RavnaPCB/01.OSOH_SOM_MB/1.DBSTM32MP1 [WIP]/Manufacturing_Data/ASSEMBLY/DBSTM32MP1-F_Fab.png

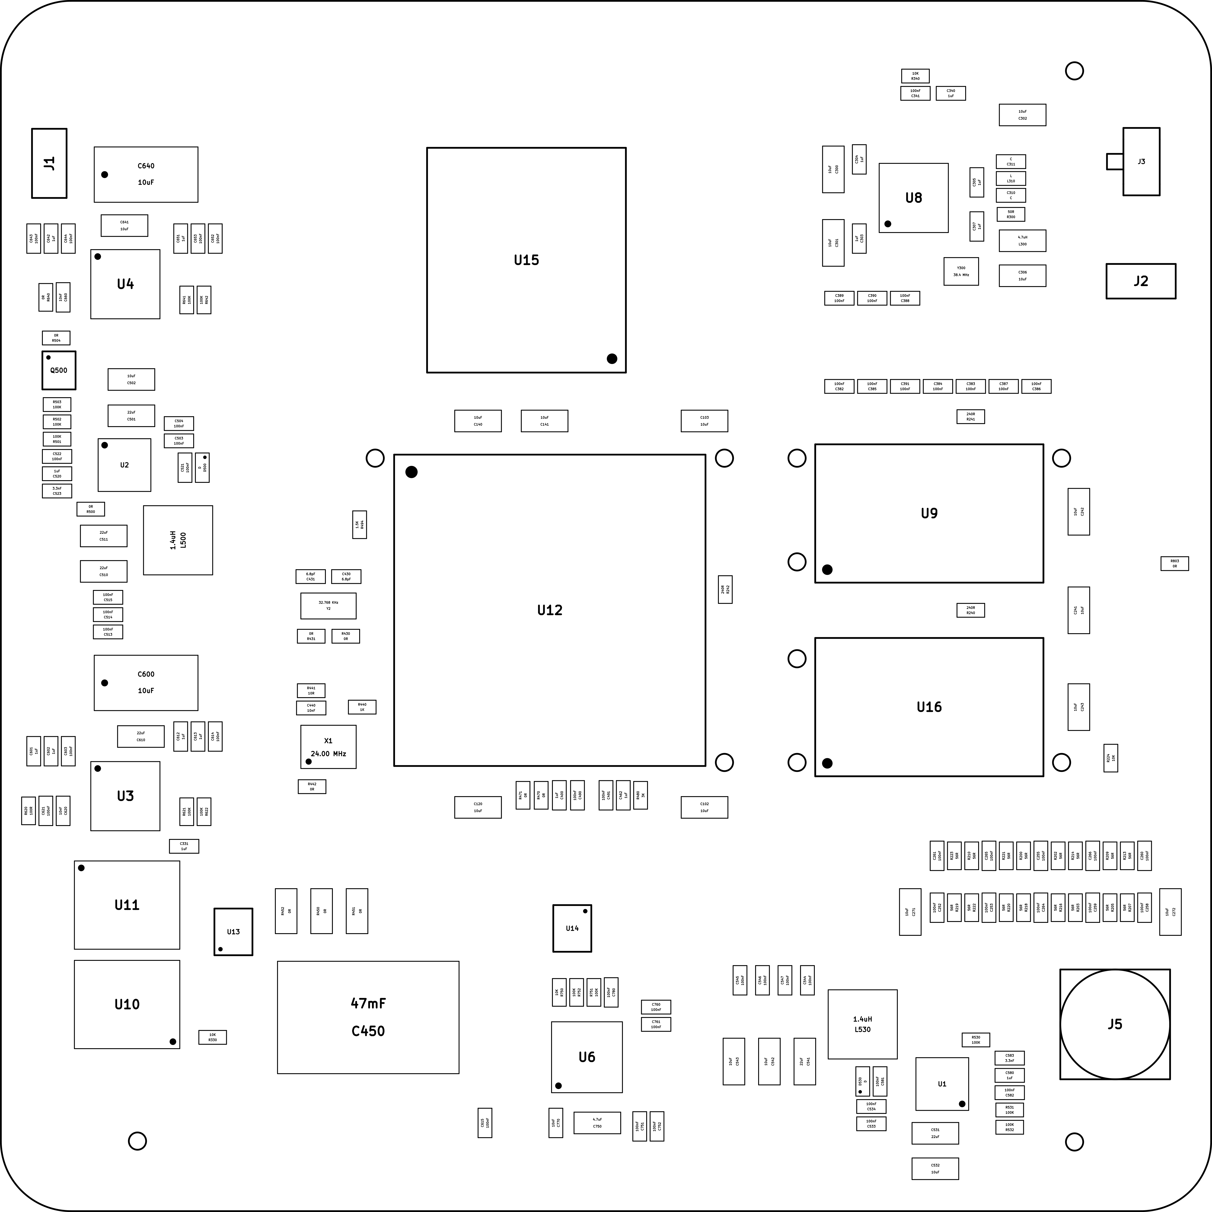
1.DBSTM32MP1 [WIP]/Manufacturing_Data/ASSEMBLY/DBSTM32MP1-F_Fab.png
