RavnaPCB/01.OSOH_SOM_MB/1.DBSTM32MP1 [WIP]/Manufacturing_Data/DP_Highlight/L3_90OHM.png

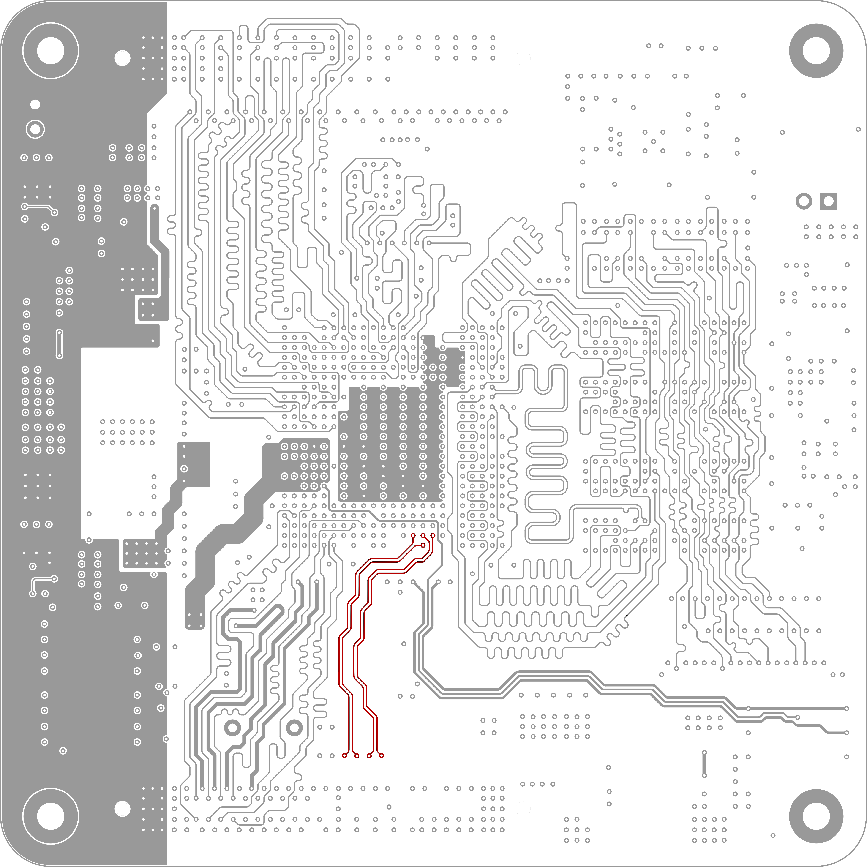
1.DBSTM32MP1 [WIP]/Manufacturing_Data/DP_Highlight/L3_90OHM.png
