RavnaPCB/01.OSOH_SOM_MB/1.DBSTM32MP1 [WIP]/HW_Development/DBSTM32MP1.kicad_sch

## KiCad design 1.DBSTM32MP1 [WIP]/HW_Development/DBSTM32MP1.kicad_sch (2022-04-24)

Schematic: DBSTM32MP1.kicad_sch

Parts:
C100, C101, C102, C103, C120, C140, C141, C241, C242, C243, C270, C271, C272, C273, C300, C301, C302, C306, C332, C502, C512, C532, C542, C543, C611, C641, C700, C710, C800: 10uF; C_0805
C104, C105, C106, C107, C108, C109, C110, C111, C112, C113, C114, C115, C116, C130, C131, C132, C133, C134, C135, C136, C142, C143, C144, C145, C146, C147, C148, C149, C150, C151, C152, C153, C154, C303, C304, C305, C307, C330, C331, C340, C400, C460, C462, C480, C520, C580, C601, C602, C612, C613, C642, C651, C701, C801: 1uF; C_0402
C200, C201, C202, C203, C204, C205, C206, C207, C208, C209, C210, C211, C212, C213, C220, C221, C222, C223, C224, C225, C226, C227, C228, C229, C230, C231, C232, C233, C240, C250, C251, C252, C253, C254, C255, C256, C257, C258, C259, C260, C261, C262, C263, C264, C265, C266, C267, C341, C350, C351, C352, C353, C354, C355, C356, C370, C371, C372, C373, C374, C375, C376, C377, C378, C379, C380, C381, C382, C383, C384, C385, C386, C387, C388, C389, C390, C391, C392, C393, C461, C470, C490, C491, C503, C504, C513, C514, C515, C521, C522, C533, C534, C544, C545, C546, C547, C581, C582, C603, C614, C615, C621, C643, C644, C652, C653, C654, C656, C702, C703, C704, C711, C712, C713, C714, C721, C751, C752, C760, C761, C780, C802, C803, C810: 100nF; C_0402
C310, C311, C820, C830: C; C_0402
C357, C360: 2.2uF; C_0805
C430, C431: 6.8pF; C_0402
C440, C620, C660, C720, C770: 10nF; C_0402
C450: 47mF; FM0H104ZF
C500, C530, C540: 22uF; CP_2312
C501, C510, C511, C531, C541, C610, C650: 22uF; C_0805
C523, C583: 3.3nF; C_0402
C600, C640: 10uF; CP_2312
C750: 4.7uF; C_0805
D420: RED; LED_0402
D421: BLUE; LED_0402
D500, D530: D; D_0402
FID1, FID2, FID3, FID4, FID5, FID6, FID7, FID8, FID9, FID10, FID11, FID12: Fiducial Marker
H1, H2, H3, H4: MountingHole_Pad; MountingHole-[2.2]-PAD-M2
J2: Connector_1x2; 1x02-Connector-[P2.00_V]
J3: Coax; CONUFL001-SMD-T
J4: uSD_693072010801
J5: Coax; SMA-132134-10
J6, J8: FX10A-120S-P-SV; FX10A-120P-SV
J7: Connector_2x5; 2x05-Connector-[P1.00_V]
L300: 4.7uH; C_0805
L310: L; C_0402
L460: 4.7uH; R_0805
L500, L530: 1.4uH; XGL-4040
Q500: N_MOSFET; SOT-323_SC-70
R200, R201, R202, R203, R204, R205, R206, R207, R208, R209, R210, R211, R212, R213, R214, R215, R216, R217, R218, R219, R220, R221, R222, R223: 56R; R_0402
R224, R225, R330, R340, R350, R351, R352, R353, R750: 10K; R_0402
R226, R620: 100R; R_0402
R240, R241, R242: 240R; R_0402
R300: 50R; R_0402
R331, R354: 22R; R_0402
R332, R355, R400, R402, R403, R405, R406, R408, R409, R410, R411, R412, R430, R431, R442, R470, R471, R500, R504, R640, R803, R900: 0R; R_0402
R401, R404, R407, R440: 1K; R_0402
R420, R421: 220R; R_0402
R441: 10R; R_0402
R450, R451, R452, R460: 0R; R_0805
R480: 3K; R_0402
R490, R491, R492, R493, R494, R495: 1.5K; R_0402
R501, R502, R503, R530, R531, R532, R621, R622, R641, R642, R721, R722, R751, R752: 100K; R_0402
R720: R100; R_0402
R800, R801: R; R_0402
TP1, TP2, TP3, TP4, TP5, TP6, TP7, TP8, TP9, TP10, TP11, TP12, TP13, TP14, TP15, TP16, TP17, TP21, TP22: TP; TP-[R0402-PAD]
TP18, TP19, TP20: TP; SP-[2.0x0.6]
U1, U2: RT6206; WDFN-10L-[3x3]-[P0.5]
U3, U4, U5: LP38798; WSON-12-[4x4]-[P0.5]
U6: LP3878-ADJ; WSON-08-[4x4]-[P0.8]
U7: LP2998; DFN-10-[3x3]-[P0.5]
U8: WF200SD; QFN-32-[4x4]-[P0.4]
U9, U16: DDR3L; TFBGA96
U10, U11: WSON-8-6x5-FLASH; WSON-08-[6x5]-[P1.27]
U12: STM32MP157AAA3
U13, U14: AND_GATE; SOT-353_SC-70-5
U15: eMMC; WFBGA153
X1: 24.00 MHz; OSC-[3.2x2.5]
Y2: 32.768 KHz; OSC-[3.2x1.5]
Y300: 38.4 MHz; OSC-[2.0x1.6]

Connections:
ADJ: C780.2, R751.1, R752.2, U6.6 (ADJ)
ANA0: U12.R4 (ANA0)
ANA1: J5.1 (In), U12.T5 (ANA1)
CPU_VDD: C120.1, C130.1, C131.1, C132.1, C133.1, C134.1, C135.1, C136.1, C353.1, C354.1, C355.1, C610.1, C611.1, C612.1, C613.1, C614.1, C615.1, R350.1, R351.1, R352.1, R353.1, R401.2, R404.2, R407.2, R409.2, R411.2, R441.2, R450.1, R460.1, R471.1, R490.1, R491.1, R492.1, R493.1, R494.1, R495.1, U3.10 (OUT_FB), U3.11 (OUT), U3.12 (OUT), U12.A14 (VDD_DSI), U12.D18 (VDD_PLL2), U12.M6 (VDD_PLL), U12.M9 (VDD), U12.N5 (VDD_ANA), U12.N8 (VDD), U12.N10 (VDD), U12.P9 (VDD), U12.P11 (VDD), U12.R10 (VDD), U12.R12 (VDD), U12.T13 (VDD), U12.U9 (VDD), U12.U12 (VDD), U12.U14 (VDD), U13.5 (VDD), U14.5 (VDD), U15.C6 (VCCQ), U15.M4 (VCCQ), U15.N4 (VCCQ), U15.P3 (VCCQ), U15.P5 (VCCQ)
DAC_EXTI9: U12.M2 (PD9)
DAC_OUT1: U12.V6 (PA4)
DAC_OUT2: U12.U5 (PA5)
DCMI_D00: J6.71, U12.E6 (PH9)
DCMI_D01[TIM5_CH1]: J6.86, U12.B1 (PH10)
DCMI_D02: J6.67, U12.C5 (PE0)
DCMI_D03: J6.73, U12.D7 (PE1)
DCMI_D04[TIM8_CH2N]: J6.65, U12.C2 (PH14)
DCMI_D05: J6.54, U12.J6 (PI4)
DCMI_D06[TIM8_CH2]: J6.64, U12.G5 (PI6)
DCMI_D07: J6.66, U12.F1 (PI7)
DCMI_D08: J6.79, U12.V11 (PH6)
DCMI_D09[TIM8_CH4]: J6.72, U12.E1 (PI2)
DCMI_D10[TIM8_ETR]: J6.76, U12.E3 (PI3)
DCMI_D11: J6.88, U12.C1 (PH15)
DCMI_D12: J6.58, U12.W8 (PF11)
DCMI_D13[TIM5_CH4]: J6.78, U12.D1 (PI0)
DCMI_HSYNC[TIM5_ETR]: J6.77, U12.D6 (PH8)
DCMI_PXCLK: J6.60, U12.W9 (PA6)
DCMI_VSYNC[TIM8_CH1]: J6.70, U12.F2 (PI5)
DDR3_A00: R200.2, U9.N3 (A00), U12.K19 (DDR_A0), U16.N3 (A00)
DDR3_A01: R201.2, U9.P7 (A01), U12.M18 (DDR_A1), U16.P7 (A01)
DDR3_A02: R202.2, U9.P3 (A02), U12.J18 (DDR_A2), U16.P3 (A02)
DDR3_A03: R203.2, U9.N2 (A03), U12.J19 (DDR_A3), U16.N2 (A03)
DDR3_A04: R204.2, U9.P8 (A04), U12.T18 (DDR_A4), U16.P8 (A04)
DDR3_A05: R205.2, U9.P2 (A05), U12.H19 (DDR_A5), U16.P2 (A05)
DDR3_A06: R206.2, U9.R8 (A06), U12.U19 (DDR_A6), U16.R8 (A06)
DDR3_A07: R207.2, U9.R2 (A07), U12.F18 (DDR_A7), U16.R2 (A07)
DDR3_A08: R208.2, U9.T8 (A08), U12.U18 (DDR_A8), U16.T8 (A08)
DDR3_A09: R209.2, U9.R3 (A09), U12.H18 (DDR_A9), U16.R3 (A09)
DDR3_A10: R210.2, U9.L7 (A10), U12.N18 (DDR_A10), U16.L7 (A10)
DDR3_A11: R211.2, U9.R7 (A11), U12.P19 (DDR_A11), U16.R7 (A11)
DDR3_A12: R212.2, U9.N7 (A12), U12.N19 (DDR_A12), U16.N7 (A12)
DDR3_A13: R213.2, U9.T3 (A13), U12.G18 (DDR_A13), U16.T3 (A13)
DDR3_A14: R214.2, U9.T7 (A14), U12.P18 (DDR_A14), U16.T7 (A14)
DDR3_A15: R215.2, U9.M7 (A15), U12.M19 (DDR_A15), U16.M7 (A15)
DDR3_BA0: R216.2, U9.M2 (BA0), U12.K20 (DDR_BA0), U16.M2 (BA0)
DDR3_BA1: R217.2, U9.N8 (BA1), U12.R18 (DDR_BA1), U16.N8 (BA1)
DDR3_BA2: R218.2, U9.M3 (BA2), U12.K18 (DDR_BA2), U16.M3 (BA2)
DDR3_CASn: R220.2, U9.K3 (CASn), U12.M22 (DDR_CASN), U16.K3 (CASn)
DDR3_CKE: R225.2, U9.K9 (CKE), U12.R19 (DDR_CKE), U16.K9 (CKE)
DDR3_CLKN: R226.2, U9.K7 (CKN), U12.N21 (DDR_CLKN), U16.K7 (CKN)
DDR3_CLKP: R226.1, U9.J7 (CKP), U12.N20 (DDR_CLKP), U16.J7 (CKP)
DDR3_CSn: R221.2, U9.L2 (CSn), U12.L18 (DDR_CSN), U16.L2 (CSn)
DDR3_DQ00: U12.E21 (DDR_DQ0), U16.E3 (DQ00)
DDR3_DQ01: U12.F21 (DDR_DQ1), U16.F7 (DQ01)
DDR3_DQ02: U12.H21 (DDR_DQ2), U16.G2 (DQ06)
DDR3_DQ03: U12.E20 (DDR_DQ3), U16.F8 (DQ03)
DDR3_DQ04: U12.J21 (DDR_DQ4), U16.H3 (DQ04)
DDR3_DQ05: U12.H20 (DDR_DQ5), U16.H7 (DQ07)
DDR3_DQ06: U12.H22 (DDR_DQ6), U16.F2 (DQ02)
DDR3_DQ07: U12.G19 (DDR_DQ7), U16.H8 (DQ05)
DDR3_DQ08: U12.N22 (DDR_DQ8), U16.D7 (DQ08)
DDR3_DQ09: U12.R21 (DDR_DQ9), U16.A7 (DQ12)
DDR3_DQ10: U12.P21 (DDR_DQ10), U16.C3 (DQ09)
DDR3_DQ11: U12.T20 (DDR_DQ11), U16.C8 (DQ10)
DDR3_DQ12: U12.V20 (DDR_DQ12), U16.C2 (DQ11)
DDR3_DQ13: U12.R20 (DDR_DQ13), U16.B8 (DQ14)
DDR3_DQ14: U12.U21 (DDR_DQ14), U16.A2 (DQ13)
DDR3_DQ15: U12.V21 (DDR_DQ15), U16.A3 (DQ15)
DDR3_DQ16: U9.D7 (DQ08), U12.B21 (DDR_DQ16)
DDR3_DQ17: U9.C3 (DQ09), U12.D21 (DDR_DQ17)
DDR3_DQ18: U9.A3 (DQ15), U12.D22 (DDR_DQ18)
DDR3_DQ19: U9.B8 (DQ14), U12.B20 (DDR_DQ19)
DDR3_DQ20: U9.C8 (DQ10), U12.A20 (DDR_DQ20)
DDR3_DQ21: U9.A7 (DQ12), U12.A21 (DDR_DQ23)
DDR3_DQ22: U9.C2 (DQ11), U12.D20 (DDR_DQ22)
DDR3_DQ23: U9.A2 (DQ13), U12.E22 (DDR_DQ21)
DDR3_DQ24: U9.E3 (DQ00), U12.V22 (DDR_DQ24)
DDR3_DQ25: U9.F7 (DQ01), U12.W20 (DDR_DQ25)
DDR3_DQ26: U9.F2 (DQ02), U12.AB21 (DDR_DQ26)
DDR3_DQ27: U9.G2 (DQ06), U12.AB20 (DDR_DQ27)
DDR3_DQ28: U9.H3 (DQ04), U12.AA21 (DDR_DQ28)
DDR3_DQ29: U9.H7 (DQ07), U12.AA20 (DDR_DQ29)
DDR3_DQ30: U9.F8 (DQ03), U12.W22 (DDR_DQ30)
DDR3_DQ31: U9.H8 (DQ05), U12.W21 (DDR_DQ31)
DDR3_DQM0: U12.G20 (DDR_DQM0), U16.E7 (LDM)
DDR3_DQM1: U12.T21 (DDR_DQM1), U16.D3 (UDM)
DDR3_DQM2: U9.D3 (UDM), U12.C22 (DDR_DQM2)
DDR3_DQM3: U9.E7 (LDM), U12.AA22 (DDR_DQM3)
DDR3_DQS0N: U12.G21 (DDR_DQS0N), U16.G3 (LDQSn)
DDR3_DQS0P: U12.G22 (DDR_DQS0P), U16.F3 (LDQS)
DDR3_DQS1N: U12.R22 (DDR_DQS1N), U16.B7 (UDQSn)
DDR3_DQS1P: U12.T22 (DDR_DQS1P), U16.C7 (UDQS)
DDR3_DQS2N: U9.B7 (UDQSn), U12.B22 (DDR_DQS2N)
DDR3_DQS2P: U9.C7 (UDQS), U12.C21 (DDR_DQS2P)
DDR3_DQS3N: U9.G3 (LDQSn), U12.Y22 (DDR_DQS3N)
DDR3_DQS3P: U9.F3 (LDQS), U12.Y21 (DDR_DQS3P)
DDR3_ODT: R223.2, U9.K1 (ODT), U12.L21 (DDR_ODT), U16.K1 (ODT)
DDR3_RASn: R219.2, U9.J3 (RASn), U12.M20 (DDR_RASN), U16.J3 (RASn)
DDR3_RESET: R224.2, U9.T2 (RESET#), U12.F19 (DDR_RESETN), U16.T2 (RESET#)
DDR3_WEn: R222.2, U9.L3 (WEn), U12.M21 (DDR_WEN), U16.L3 (WEn)
DSI_CKN: J6.105, U12.A16 (DSI_CKN)
DSI_CKP: J6.109, U12.B16 (DSI_CKP)
DSI_D0N: J6.97, U12.A15 (DSI_D0N)
DSI_D0P: J6.101, U12.B15 (DSI_D0P)
DSI_D1N: J6.113, U12.A17 (DSI_D1N)
DSI_D1P: J6.117, U12.B17 (DSI_D1P)
ETH_CLK: J8.32, U12.Y8 (PG8)
ETH_COL: J8.36, U12.T4 (PA3)
ETH_CRS: J8.40, U12.AA3 (PA0)
ETH_GTXCLK: J8.44, U12.AB4 (PG4)
ETH_MDC: J8.52, U12.AB3 (PC1)
ETH_MDIO: J8.56, U12.AB2 (PA2)
ETH_RXCLK: J8.24, U12.V4 (PA1)
ETH_RXD00: J8.31, U12.AB6 (PC4)
ETH_RXD01: J8.27, U12.AA6 (PC5)
ETH_RXD02: J8.23, U12.AB5 (PB0)
ETH_RXD03: J8.19, U12.W2 (PH7)
ETH_RXDV: J8.28, U12.Y9 (PA7)
ETH_RXER: J8.20, U12.W1 (PI10)
ETH_TXCLK: J8.51, U12.U3 (PC3)
ETH_TXD00: J8.35, U12.AA1 (PG13)
ETH_TXD01: J8.39, U12.AA2 (PG14)
ETH_TXD02: J8.43, U12.Y1 (PC2)
ETH_TXD03: J8.47, U12.Y2 (PE2)
ETH_TXEN: J8.55, U12.Y5 (PB11)
ETH_TXER: J8.48, U12.V3 (PF3)
FDCAN1_RX: J8.100, U12.Y16 (PA11)
FDCAN1_TX: J8.98, U12.W16 (PA12)
GND: C100.2, C101.2, C102.2, C103.2, C104.2, C105.2, C106.2, C107.2, C108.2, C109.2, C110.2, C111.2, C112.2, C113.2, C114.2, C115.2, C116.2, C120.2, C130.2, C131.2, C132.2, C133.2, C134.2, C135.2, C136.2, C140.2, C141.2, C142.2, C143.2, C144.2, C145.2, C146.2, C147.2, C148.2, C149.2, C150.2, C151.2, C152.2, C153.2, C154.2, C200.2, C201.2, C202.2, C203.2, C204.2, C205.2, C206.2, C207.2, C208.2, C209.2, C210.2, C211.2, C212.2, C213.2, C220.2, C221.2, C222.2, C223.2, C224.2, C225.2, C226.2, C227.2, C228.2, C229.2, C230.2, C231.2, C232.2, C233.2, C240.2, C241.2, C242.2, C243.2, C250.2, C251.2, C252.2, C253.2, C254.2, C255.2, C256.2, C257.2, C258.2, C259.2, C260.2, C261.2, C262.2, C263.2, C264.2, C265.2, C266.2, C267.2, C270.2, C271.2, C272.2, C273.2, C300.2, C301.2, C302.2, C303.2, C304.2, C305.2, C306.2, C307.2, C310.2, C311.2, C330.2, C331.2, C332.2, C340.2, C341.2, C350.2, C351.2, C352.2, C353.2, C354.2, C355.2, C356.2, C357.2, C360.1, C370.2, C371.2, C372.2, C373.2, C374.2, C375.2, C376.2, C377.2, C378.2, C379.2, C380.2, C381.2, C382.2, C383.2, C384.2, C385.2, C386.2, C387.2, C388.2, C389.2, C390.2, C391.2, C392.2, C393.2, C400.2, C430.1, C431.1, C440.2, C450.2, C460.2, C461.2, C462.1, C470.1, C480.1, C490.2, C491.2, C500.2, C501.2, C502.2, C503.2, C504.2, C510.2, C511.2, C512.2, C513.2, C514.2, C515.2, C520.2, C523.2, C530.2, C531.2, C532.2, C533.2, C534.2, C540.2, C541.2, C542.2, C543.2, C544.2, C545.2, C546.2, C547.2, C580.2, C583.2, C600.2, C601.2, C602.2, C603.2, C610.2, C611.2, C612.2, C613.2, C614.2, C615.2, C620.2, C621.2, C640.2, C641.2, C642.2, C643.2, C644.2, C650.2, C651.2, C652.2, C653.2, C654.2, C656.2, C660.2, C700.2, C701.2, C702.2, C703.2, C704.2, C710.2, C711.2, C712.2, C713.2, C714.2, C720.2, C721.2, C750.2, C751.2, C752.2, C760.2, C761.2, C770.2, C800.2, C801.2, C802.2, C803.2, C810.2, C820.2, C830.2, D420.2 (A), D421.2 (A), H1.1, H2.1, H3.1, H4.1, J2.2, J3.2 (Ext), J4.6 (VSS), J5.2 (Ext), J6.11, J6.12, J6.13, J6.14, J6.15, J6.20, J6.21, J6.26, J6.27, J6.32, J6.33, J6.38, J6.39, J6.44, J6.45, J6.50, J6.51, J6.56, J6.57, J6.62, J6.63, J6.68, J6.69, J6.74, J6.75, J6.80, J6.81, J6.84, J6.87, J6.90, J6.91, J6.93, J6.95, J6.96, J6.99, J6.102, J6.103, J6.107, J6.108, J6.111, J6.114, J6.115, J6.119, J6.120, J7.7, J7.8, J8.11, J8.12, J8.13, J8.14, J8.15, J8.16, J8.17, J8.18, J8.21, J8.22, J8.25, J8.26, J8.29, J8.30, J8.33, J8.34, J8.37, J8.38, J8.41, J8.42, J8.45, J8.46, J8.49, J8.50, J8.53, J8.54, J8.57, J8.58, J8.62, J8.63, J8.66, J8.69, J8.70, J8.74, J8.75, J8.78, J8.81, J8.82, J8.84, J8.87, J8.91, J8.93, J8.94, J8.95, J8.96, J8.97, J8.99, J8.101, J8.102, J8.103, J8.105, J8.107, J8.109, Q500.3 (D), R224.1, R225.1, R240.1, R241.1, R242.1, R300.1, R340.2, R402.2, R405.2, R408.2, R410.2, R412.2, R440.2, R470.1, R480.1, R502.1, R532.1, R622.1, R642.1, R722.1, R750.1, R752.1, TP20.1, U3.6 (GND_CP), U3.7 (GND), U3.13 (GND), U4.6 (GND_CP), U4.7 (GND), U4.13 (GND), U5.6 (GND_CP), U5.7 (GND), U5.13 (GND), U6.3 (GND), U7.3 (AGND), U7.8 (PGND), U7.11 (PAD), U8.10 (GND), U8.14 (RESERVE_1), U8.33 (GND), U9.A9 (VSS), U9.B1 (VSSQ), U9.B3 (VSS), U9.B9 (VSSQ), U9.D1 (VSSQ), U9.D8 (VSSQ), U9.E1 (VSS), U9.E2 (VSSQ), U9.E8 (VSSQ), U9.F9 (VSSQ), U9.G1 (VSSQ), U9.G8 (VSS), U9.G9 (VSSQ), U9.J2 (VSS), U9.J8 (VSS), U9.M1 (VSS), U9.M9 (VSS), U9.P1 (VSS), U9.P9 (VSS), U9.T1 (VSS), U9.T9 (VSS), U10.4 (GND), U11.4 (GND), U12.A1 (VSS), U12.A19 (VSS), U12.A22 (VSS), U12.AA4 (VSS), U12.AA13 (VSS_USBHS), U12.AA16 (VSS_USBHS), U12.AA18 (VSS), U12.AB1 (VSS), U12.AB18 (VSS), U12.AB22 (VSS), U12.B2 (VSS), U12.B19 (VSS), U12.C3 (VSS), U12.C8 (VSS), U12.C11 (VSS), U12.C14 (VSS_DSI), U12.C15 (VSS_DSI), U12.C16 (VSS_DSI), U12.C17 (VSS_DSI), U12.C18 (VSS_DSI), U12.C19 (VSS), U12.C20 (VSS), U12.D4 (VSS), U12.D19 (VSS_PLL2), U12.E5 (VSS), U12.E19 (VSS), U12.F6 (VSS), U12.F7 (VSS), U12.F8 (VSS), U12.F16 (VSS), U12.F20 (VSS), U12.G4 (VSS), U12.G6 (VSS), U12.G8 (VSS), U12.G10 (VSS), U12.G12 (VSS), U12.G14 (VSS), U12.G17 (VSS), U12.H7 (VSS), U12.J9 (VSS), U12.J11 (VSS), U12.J13 (VSS), U12.J17 (VSS), U12.J20 (VSS), U12.K3 (VSS), U12.K7 (VSS), U12.K10 (VSS), U12.K12 (VSS), U12.K14 (VSS), U12.L9 (VSS), U12.L11 (VSS), U12.L13 (VSS), U12.L17 (VSS), U12.L19 (VSS), U12.L20 (VSS), U12.M5 (VSS_PLL), U12.M7 (VSS), U12.M10 (VSS), U12.M12 (VSS), U12.M14 (VSS), U12.N6 (VREF-), U12.N9 (VSS), U12.N11 (VSS), U12.N13 (VSS), U12.N17 (VSS), U12.P3 (VSS), U12.P5 (VSS_ANA), U12.P7 (VSS), U12.P10 (VSS), U12.P12 (VSS), U12.P14 (VSS), U12.P20 (VSS), U12.R6 (VSSA), U12.R8 (VSS), U12.R17 (VSS), U12.T6 (VSSA), U12.T7 (VSS), U12.T9 (VSS), U12.T11 (VSS), U12.T19 (VSS), U12.U6 (VSSA), U12.U7 (VSS), U12.U13 (VSS), U12.U15 (VSS), U12.U17 (VSS), U12.U20 (VSS), U12.V5 (VSS), U12.V16 (VSS), U12.V18 (VSS), U12.V19 (VSS), U12.W17 (VSS), U12.W19 (VSS), U12.Y3 (VSS), U12.Y7 (VSS), U12.Y10 (VSS), U12.Y13 (VSS_USBHS), U12.Y14 (VSS_USBHS), U12.Y15 (VSS_USBHS), U12.Y18 (VSS), U12.Y20 (VSS), U13.3 (GND), U14.3 (GND), U15.A6 (VSS), U15.C4 (VSSQ), U15.E7 (VSS), U15.G5 (VSS), U15.H10 (VSS), U15.J5 (VSS), U15.K8 (VSS), U15.N2 (VSSQ), U15.N5 (VSSQ), U15.P4 (VSSQ), U15.P6 (VSSQ), U16.A9 (VSS), U16.B1 (VSSQ), U16.B3 (VSS), U16.B9 (VSSQ), U16.D1 (VSSQ), U16.D8 (VSSQ), U16.E1 (VSS), U16.E2 (VSSQ), U16.E8 (VSSQ), U16.F9 (VSSQ), U16.G1 (VSSQ), U16.G8 (VSS), U16.G9 (VSSQ), U16.J2 (VSS), U16.J8 (VSS), U16.M1 (VSS), U16.M9 (VSS), U16.P1 (VSS), U16.P9 (VSS), U16.T1 (VSS), U16.T9 (VSS), X1.2 (GND), Y300.2, Y300.4
GPIO[TIM8_CH3N]: J6.82, U12.E7 (PK1)
GPIO_00[BOTTOM]: U12.W5 (PG0)
GPIO_00[TOP]: U12.H3 (PZ7)
GPIO_01[BOTTOM]: U12.Y4 (PG1)
GPIO_01[TOP]: U12.J5 (PI9)
GPIO_02[BOTTOM]: U12.W4 (PG2)
GPIO_02[TOP]: U12.K6 (PJ11)
GPIO_03[BOTTOM]: U12.U4 (PG3)
GPIO_03[TOP]: U12.L3 (PD6)
GPIO_04[BOTTOM]: U12.AA5 (PB1)
GPIO_04[TOP]: U12.M1 (PD8)
GPIO_05[BOTTOM]: U12.W7 (PF13)
GPIO_05[TOP]: U12.M3 (PD14)
GPIO_06[BOTTOM]: U12.U8 (PG5)
GPIO_06[TOP]: U12.L1 (PD15)
GPIO_07[BOTTOM]: U12.V8 (PF12)
GPIO_07[TOP]: U12.K2 (PJ4)
GPIO_08[BOTTOM]: U12.AA8 (PB5)
GPIO_08[TOP]: U12.K1 (PJ5)
GPIO_09[BOTTOM]: U12.AB8 (PB8)
GPIO_09[TOP]: U12.L5 (PJ6)
GPIO_10[BOTTOM]: U12.AB9 (PD11)
GPIO_10[TOP]: U12.L2 (PJ9)
GPIO_11[BOTTOM]: U12.W10 (PE7)
GPIO_11[TOP]: U12.C7 (PJ15)
GPIO_12[BOTTOM]: U12.W11 (PE9)
GPIO_13[BOTTOM]: U12.Y12 (PE8)
GPIO_14[BOTTOM]: U12.V14 (PD13)
GPIO_15[BOTTOM]: U12.W14 (PE10)
GPIO_16[BOTTOM]: U12.W15 (PG9)
GPIO_FEM_1: TP11.1, U8.1 (GPIO/FEM_1)
GPIO_FEM_2: TP12.1, U8.2 (GPIO/FEM_2)
GPIO_FEM_3: TP13.1, U8.3 (GPIO/FEM_3)
GPIO_FEM_4: TP14.1, U8.4 (GPIO/FEM_4)
GPIO_FEM_5: TP15.1, U8.17 (GPIO/FEM_5)
GPIO_FEM_6: TP16.1, U8.18 (GPIO/FEM_6)
GPIO_FEM_PDET: TP10.1, U8.5 (GPIO/FEM_PDET)
GPIO_PTA_FREQ: TP6.1, U8.22 (GPIO/PTA_FREQ)
GPIO_PTA_RF_ACT: TP8.1, U8.20 (GPIO/PTA_RF_ACT)
GPIO_PTA_STATUS: TP7.1, U8.21 (GPIO/PTA_STATUS)
GPIO_PTA_TX_CONF: TP9.1, U8.19 (GPIO/PTA_TX_CONF)
HDMI-CEC: J6.61, U12.E11 (PA15)
I2C1_SCL: J8.60, R490.2, U12.V7 (PF14)
I2C1_SDA: J8.64, R491.2, U12.W6 (PF15)
I2C2_SCL: J6.83, R492.2, U12.A3 (PH4)
I2C2_SDA: J6.85, R493.2, U12.A2 (PH5)
I2C4_SCL: J6.112, R494.2, U12.G1 (PZ4)
I2C4_SDA: J6.110, R495.2, U12.H4 (PZ5)
I2S1_CK: J6.89, U12.G2 (PZ0)
I2S1_MCK: J6.100, U12.G3 (PZ6)
I2S1_SDI: J6.94, U12.H5 (PZ1)
I2S1_SDO: J6.98, U12.K5 (PZ2)
I2S1_WS: J6.92, U12.F4 (PZ3)
I2S_CLKIN: U12.T3 (PI11)
JTCK-SWCLK: J7.4, U12.D17 (JTCK-SWCLK)
JTDI: J7.1, U12.D16 (JTDI)
JTDO-TRACESWO: J7.3, U12.E16 (JTDO-TRACESWO)
JTMS-SWDIO: J7.6, U12.E17 (JTMS-SWDIO)
LTDC-B00: J6.40, U12.B8 (PJ12)
LTDC-B01: J6.42, U12.J4 (PG12)
LTDC-B02: J6.41, U12.B7 (PJ14)
LTDC-B03: J6.59, U12.A8 (PD10)
LTDC-B04: J6.46, U12.B6 (PK3)
LTDC-B05: J6.48, U12.A6 (PK4)
LTDC-B06: J6.47, U12.C6 (PK5)
LTDC-B07: J6.49, U12.A5 (PK6)
LTDC-CLK: J6.37, U12.D2 (PI14)
LTDC-DE: J6.53, U12.B5 (PK7)
LTDC-G00: J6.28, U12.L4 (PJ7)
LTDC-G01: J6.30, U12.H6 (PJ8)
LTDC-G02[TIM8_CH1N]: J6.36, U12.D3 (PH13)
LTDC-G03: J6.31, U12.J3 (PJ10)
LTDC-G04: J6.34, U12.A7 (PJ13)
LTDC-G05[TIM8_CH3]: J6.55, U12.D8 (PK0)
LTDC-G06[TIM8_BKIN2]: J6.35, U12.E2 (PI1)
LTDC-G07[TIM8_BKIN1]: J6.52, U12.E8 (PK2)
LTDC-HSYNC: J6.25, U12.H2 (PI12)
LTDC-R00: J6.16, U12.F3 (PI15)
LTDC-R01: J6.18, U12.J2 (PJ0)
LTDC-R02: J6.17, U12.L6 (PJ1)
LTDC-R03: J6.19, U12.K4 (PJ2)
LTDC-R04: J6.22, U12.J1 (PJ3)
LTDC-R05[TIM5_CH2]: J6.43, U12.B3 (PH11)
LTDC-R06[TIM5_CH3]: J6.23, U12.F5 (PH12)
LTDC-R07: J6.24, U12.C4 (PE15)
LTDC-VSYNC: J6.29, U12.H1 (PI13)
NJTRST: J7.5, U12.E15 (NJTRST)
NRST: J8.89, R900.2, U12.R2 (NRST), U13.2
NRST_CORE: R900.1, U12.R1 (NRST_CORE)
unnamed: C306.1, C307.1, L300.2, U8.9 (VDD_RF)
unnamed: C310.1, L310.2, U8.12 (RF_2)
unnamed: C311.1, J3.1 (In), L310.1
unnamed: C356.1, C357.1, U15.C2 (VDDI)
unnamed: C400.1, TP21.1, U12.AB12 (VDDA1V8_REG), U14.1, U14.2
unnamed: C430.2, R430.2, Y2.2
unnamed: C431.2, R431.2, Y2.1
unnamed: C450.1, R451.1
unnamed: C462.2, U12.AB17 (VDDA1V1_REG)
unnamed: C470.2, U12.B14 (VDDA1V8_DSI)
unnamed: C480.2, U12.A18 (VDD1V2_DSI_PHY), U12.B18 (VDD1V2_DSI_REG)
unnamed: C521.2, D500.1 (K), U2.8 (BOOT)
unnamed: C522.2, R501.1, R502.2, R503.2, U2.2 (FB)
unnamed: C581.2, D530.1 (K), U1.8 (BOOT)
unnamed: C582.2, R531.1, R532.2, U1.2 (FB)
unnamed: C620.1, U3.4 (CP)
unnamed: C621.1, R620.1, U3.5 (EN)
unnamed: C660.1, U4.4 (CP)
unnamed: C720.1, U5.4 (CP)
unnamed: C721.1, R720.1, U5.5 (EN)
unnamed: C770.1, U6.1 (Bypass)
unnamed: C820.1, R800.1, U7.2 (BIAS)
unnamed: C830.1, R801.1, U7.4 (VDDQ)
unnamed: D420.1 (K), R420.1
unnamed: D421.1 (K), R421.1
unnamed: Q500.1 (G), R504.2
unnamed: Q500.2 (S), R503.1
unnamed: R240.2, U16.L8 (ZQ)
unnamed: R241.2, U9.L8 (ZQ)
unnamed: R242.2, U12.K22 (DDR_ZQ)
unnamed: R300.2, U8.11 (RF_1)
unnamed: R331.1, U12.V12 (PF10)
unnamed: R332.2, U12.U10 (PC0)
unnamed: R351.2, R354.1, U15.M6 (CLK)
unnamed: R353.2, R355.2, U15.K5 (RSTn)
unnamed: R400.1, U12.N3 (BOOT0)
unnamed: R400.2, R401.1, R402.1
unnamed: R403.1, U12.N4 (BOOT1)
unnamed: R403.2, R404.1, R405.1
unnamed: R406.1, U12.P4 (BOOT2)
unnamed: R406.2, R407.1, R408.1
unnamed: R420.2, U12.W3 (PA13)
unnamed: R421.2, U12.R3 (PA14)
unnamed: R430.1, U12.P1 (PC14-OSC32_IN)
unnamed: R431.1, U12.P2 (PC15-OSC32_OUT)
unnamed: R440.1, U12.T2 (PH1-OSC_OUT)
unnamed: R442.1, X1.1 (EN)
unnamed: R470.2, R471.2, U12.AA12 (BYPASS_REG1V8)
unnamed: R500.1, TP2.1, U2.5 (PGOOD)
unnamed: R530.1, TP1.1, U1.5 (PGOOD)
unnamed: R621.1, R622.2, U3.8 (FB)
unnamed: R621.2, U3.9 (SET)
unnamed: R640.1, U4.5 (EN)
unnamed: R641.1, R642.2, U4.8 (FB)
unnamed: R641.2, U4.9 (SET)
unnamed: R721.1, R722.2, U5.8 (FB)
unnamed: R721.2, U5.9 (SET)
unnamed: TP17.1, U8.23 (LP_CLK)
unnamed: U8.7 (XTAL_I), Y300.1
unnamed: U8.8 (XTAL_O), Y300.3
unnamed: U12.T1 (PH0-OSC_IN), X1.3 (OUT)
OSC_VDD: C440.1, R441.1, X1.4 (VDD)
PDR_ON: R409.1, R410.1, U12.V2 (PDR_ON)
PDR_ON_CORE: R411.1, R412.1, U12.U2 (PDR_ON_CORE)
PG: TP5.1, U7.5 (PG)
PWR_LP: R504.1, U12.U1 (PWR_LP)
PWR_ON: R442.2, U2.1 (EN), U12.V1 (PWR_ON), U13.1
PWR_ONRST: R640.2, U1.1 (EN), U7.7 (EN), U13.4
QUADSPI_BK1_IO00: U10.5 (IO0), U12.AB10 (PF8)
QUADSPI_BK1_IO01: U10.2 (IO1), U12.AB11 (PF9)
QUADSPI_BK1_IO02: U10.3 (IO2), U12.AA10 (PF7)
QUADSPI_BK1_IO03: U10.7 (IO3), U12.AA11 (PF6)
QUADSPI_BK1_NCS: R330.2, R332.1, U10.1 (CS), U11.1 (CS), U12.W13 (PB6)
QUADSPI_BK2_IO00: U11.5 (IO0), U12.AB7 (PH2)
QUADSPI_BK2_IO01: U11.2 (IO1), U12.Y6 (PH3)
QUADSPI_BK2_IO02: U11.3 (IO2), U12.AA9 (PG10)
QUADSPI_BK2_IO03: U11.7 (IO3), U12.Y11 (PG7)
QUADSPI_CLK: R331.2, U10.6 (CLK), U11.6 (CLK)
SDMMC1_CDIR: U12.F12 (PB9)
SDMMC1_CK: J4.5 (CLK), R340.1, U12.E12 (PC12)
SDMMC1_CKIN: U12.F15 (PE4)
SDMMC1_CMD: J4.3 (CMD), U12.D12 (PD2)
SDMMC1_D00: J4.7 (DAT0), U12.E14 (PC8)
SDMMC1_D01: J4.8 (DAT1), U12.D14 (PC9)
SDMMC1_D02: J4.1 (DATA2), U12.E9 (PE6)
SDMMC1_D03: J4.2 (DATA3), U12.D15 (PC11)
SDMMC1_D123DIR: U12.F14 (PC10)
SDMMC2_CK: R354.2, U12.A10 (PE3)
SDMMC2_CMD: R352.2, U12.D11 (PG6), U15.M5 (CMD)
SDMMC2_D00: R350.2, U12.A13 (PB14), U15.A3 (DATA0)
SDMMC2_D01: U12.B12 (PB15), U15.A4 (DATA1)
SDMMC2_D02: U12.A12 (PB3), U15.A5 (DATA2)
SDMMC2_D03: U12.C13 (PB4), U15.B2 (DATA3)
SDMMC2_D04: U12.B13 (PA8), U15.B3 (DATA4)
SDMMC2_D05: U12.A11 (PA9), U15.B4 (DATA5)
SDMMC2_D06: U12.C12 (PE5), U15.B5 (DATA6)
SDMMC2_D07: U12.B11 (PD3), U15.B6 (DATA7)
SDMMC2_RES: R355.1, U12.F11 (PB7)
SDMMC3_CDIR: U8.24 (GPIO_WIRQ), U12.B9 (PF1)
SDMMC3_CK: U8.26 (SDIO_CLK/SPI_CLK), U12.D10 (PG15)
SDMMC3_CKIN: U12.E10 (PF0)
SDMMC3_CMD: U8.27 (SDIO_CMD/SPI_MOSI), U12.C10 (PD0)
SDMMC3_D00: U8.28 (SDIO_DAT0/SPI_MISO), U12.B10 (PD1)
SDMMC3_D0DIR: U8.16 (GPIO/WUP), U12.F13 (PF2)
SDMMC3_D01: U8.29 (SDIO_DAT1/SPI_WIRQ), U12.C9 (PD4)
SDMMC3_D02: U8.30 (SDIO_DAT2/HIF_SEL), U12.A9 (PD5)
SDMMC3_D03: U8.31 (SDIO_DAT3/SPI_CSN), U12.F10 (PD7)
SDMMC3_D123DIR: U8.15 (RESETN), U12.F9 (PF4)
SDMMC3_RESET?: U12.D9 (PF5)
SPI4_MISO: J6.118, U12.A4 (PE13)
SPI4_MOSI: J6.116, U12.B4 (PE14)
SPI4_NSS: J6.104, U12.D5 (PE11)
SPI4_SCK: J6.106, U12.E4 (PE12)
SS: C583.1, U1.4 (SS)
SS1: C523.1, U2.4 (SS)
SW1: C581.1, L530.1, TP3.1, U1.6 (SW), U1.7 (SW)
SW2: C521.1, L500.1, TP4.1, U2.6 (SW), U2.7 (SW)
TP1: U12.AA19 (DDR_ATO)
TP2: U12.L22 (DDR_DTO0)
TP3: U12.K21 (DDR_DTO1)
USART3_CTS: J8.79, U12.V10 (PB13)
USART3_RTS: J8.77, U12.W12 (PD12)
USART3_RX: J8.73, U12.AA7 (PB12)
USART3_TX: J8.71, U12.V9 (PB10)
USART4_RX: TP18.1, U12.V13 (PB2)
USART4_TX: TP19.1, U12.U11 (PG11)
USART6_RX: J7.9, U12.D13 (PC7)
USART6_TX: J7.10, U12.E13 (PC6)
USB_D1+: J8.76, U12.AA15 (USB_DP1)
USB_D1-: J8.80, U12.AB15 (USB_DM1)
USB_D2+: J8.72, U12.AB14 (USB_DP2)
USB_D2-: J8.68, U12.AA14 (USB_DM2)
USB_OTG_ID: J8.83, U12.Y17 (PA10)
USB_REG_EN: R750.2, TP22.1, U6.8 (SD), U14.4
USB_RREF: R480.2, U12.AA17 (USB_RREF)
USB_VBUS: J8.85, U12.V15 (OTG_VBUS)
VBAT: R450.2, R451.2, R452.2, U12.M4 (VBAT)
VBAT_IN: J8.59, J8.61, R452.1
VDDA: C460.1, C461.1, L460.1, L460.2, R460.2, U12.P6 (VREF+), U12.R5 (VDDA)
VDDS_DDR: C100.1, C101.1, C102.1, C103.1, C104.1, C105.1, C106.1, C107.1, C108.1, C109.1, C110.1, C111.1, C112.1, C113.1, C114.1, C115.1, C116.1, C200.1, C201.1, C202.1, C203.1, C204.1, C205.1, C206.1, C207.1, C208.1, C209.1, C210.1, C211.1, C220.1, C221.1, C222.1, C223.1, C224.1, C225.1, C226.1, C227.1, C228.1, C229.1, C230.1, C231.1, C241.1, C242.1, C243.1, C370.1, C371.1, C372.1, C373.1, C374.1, C375.1, C376.1, C377.1, C378.1, C379.1, C380.1, C381.1, C382.1, C383.1, C384.1, C385.1, C386.1, C387.1, C388.1, C389.1, C390.1, C391.1, C392.1, C393.1, C540.1, C541.1, C542.1, C543.1, C544.1, C545.1, C546.1, C547.1, C582.1, L530.2, R531.2, R801.2, R803.1, R803.2, U9.A1 (VDDQ), U9.A8 (VDDQ), U9.B2 (VDD), U9.C1 (VDDQ), U9.C9 (VDDQ), U9.D2 (VDDQ), U9.D9 (VDD), U9.E9 (VDDQ), U9.F1 (VDDQ), U9.G7 (VDD), U9.H2 (VDDQ), U9.H9 (VDDQ), U9.K2 (VDD), U9.K8 (VDD), U9.N1 (VDD), U9.N9 (VDD), U9.R1 (VDD), U9.R9 (VDD), U12.E18 (VDDQ_DDR), U12.F17 (VDDQ_DDR), U12.G16 (VDDQ_DDR), U12.H17 (VDDQ_DDR), U12.J16 (VDDQ_DDR), U12.K17 (VDDQ_DDR), U12.L16 (VDDQ_DDR), U12.M17 (VDDQ_DDR), U12.N16 (VDDQ_DDR), U12.P17 (VDDQ_DDR), U12.R16 (VDDQ_DDR), U12.T17 (VDDQ_DDR), U12.U16 (VDDQ_DDR), U12.V17 (VDDQ_DDR), U12.W18 (VDDQ_DDR), U12.Y19 (VDDQ_DDR), U16.A1 (VDDQ), U16.A8 (VDDQ), U16.B2 (VDD), U16.C1 (VDDQ), U16.C9 (VDDQ), U16.D2 (VDDQ), U16.D9 (VDD), U16.E9 (VDDQ), U16.F1 (VDDQ), U16.G7 (VDD), U16.H2 (VDDQ), U16.H9 (VDDQ), U16.K2 (VDD), U16.K8 (VDD), U16.N1 (VDD), U16.N9 (VDD), U16.R1 (VDD), U16.R9 (VDD)
VDD_CORE: C140.1, C141.1, C142.1, C143.1, C144.1, C145.1, C146.1, C147.1, C148.1, C149.1, C150.1, C151.1, C152.1, C153.1, C154.1, C510.1, C511.1, C512.1, C513.1, C514.1, C515.1, C522.1, L500.2, R501.2, U12.H9 (VDDCORE), U12.H11 (VDDCORE), U12.H13 (VDDCORE), U12.H15 (VDDCORE), U12.J8 (VDDCORE), U12.J10 (VDDCORE), U12.J12 (VDDCORE), U12.J14 (VDDCORE), U12.K9 (VDDCORE), U12.K11 (VDDCORE), U12.K13 (VDDCORE), U12.K15 (VDDCORE), U12.L8 (VDDCORE), U12.L10 (VDDCORE), U12.L12 (VDDCORE), U12.L14 (VDDCORE), U12.M11 (VDDCORE), U12.M13 (VDDCORE), U12.M15 (VDDCORE), U12.N12 (VDDCORE), U12.N14 (VDDCORE), U12.P13 (VDDCORE), U12.P15 (VDDCORE), U12.R14 (VDDCORE), U12.T15 (VDDCORE)
VDD_PER: C300.1, C301.1, C302.1, C303.1, C304.1, C305.1, C330.1, C331.1, C332.1, C340.1, C341.1, C350.1, C351.1, C352.1, C360.2, C650.1, C651.1, C652.1, C653.1, C654.1, C656.1, J4.4 (VDD), L300.1, R330.1, U4.10 (OUT_FB), U4.11 (OUT), U4.12 (OUT), U8.13 (VDD_PA), U8.25 (VDD_DIG), U8.32 (VDD_IO), U10.8 (VCC), U11.8 (VCC), U15.E6 (VCC), U15.F5 (VCC), U15.J10 (VCC), U15.K9 (VCC)
VDD_USB: C490.1, C491.1, C760.1, C761.1, C780.1, R751.2, U6.5 (OUT), U12.AB13 (VDD3V3_USBHS), U12.AB16 (VDD3V3_USBFS)
VIN: C500.1, C501.1, C502.1, C503.1, C504.1, C530.1, C531.1, C532.1, C533.1, C534.1, C600.1, C601.1, C602.1, C603.1, C640.1, C641.1, C642.1, C643.1, C644.1, C700.1, C701.1, C702.1, C703.1, C704.1, C750.1, C751.1, C752.1, D500.2 (A), D530.2 (A), J2.1, J6.1, J6.2, J6.3, J6.4, J6.5, J6.6, J6.7, J6.8, J6.9, J6.10, J7.2, J8.1, J8.2, J8.3, J8.4, J8.5, J8.6, J8.7, J8.8, J8.9, J8.10, J8.104, J8.106, J8.108, J8.110, J8.111, J8.112, J8.113, J8.114, J8.115, J8.116, J8.117, J8.118, J8.119, J8.120, R620.2, R720.2, U1.9 (VIN), U1.10 (VIN), U2.9 (VIN), U2.10 (VIN), U3.1 (VIN), U3.2 (VIN), U3.3 (VIN_CP), U4.1 (VIN), U4.2 (VIN), U4.3 (VIN_CP), U5.1 (VIN), U5.2 (VIN), U5.3 (VIN_CP), U6.4 (VIN)
VREF_DDR: C212.1, C213.1, C232.1, C233.1, C240.1, U7.1 (VREF), U9.H1 (VREFDQ), U9.M8 (VREFCA), U12.AB19 (DDR_VREF), U16.H1 (VREFDQ), U16.M8 (VREFCA)
VREG5: C580.1, R530.2, U1.3 (VREG5)
VREG5_1: C520.1, R500.2, U2.3 (VREG5)
VTT_DDR: C250.1, C251.1, C252.1, C253.1, C254.1, C255.1, C256.1, C257.1, C258.1, C259.1, C260.1, C261.1, C262.1, C263.1, C264.1, C265.1, C266.1, C267.1, C270.1, C271.1, C272.1, C273.1, C810.1, R200.1, R201.1, R202.1, R203.1, R204.1, R205.1, R206.1, R207.1, R208.1, R209.1, R210.1, R211.1, R212.1, R213.1, R214.1, R215.1, R216.1, R217.1, R218.1, R219.1, R220.1, R221.1, R222.1, R223.1, U7.6 (SNS), U7.9 (VTT)
VTT_IN: C710.1, C711.1, C712.1, C713.1, C714.1, C800.1, C801.1, C802.1, C803.1, R800.2, U5.10 (OUT_FB), U5.11 (OUT), U5.12 (OUT), U7.10 (VIN)
WKUP3-TAMPOUT2: J8.67, U12.N2 (PC13)
WKUP4-TAMPIN2: J8.65, U12.N1 (PI8)

Notes on the sheet:
5. VDS:
- PWR_ONRST IS ALSO FORCED LOW TOGETHER WITH PWR_ON
- THE SOFTWARE PREPARES FOR STANDBY ENTRY (STOPS SOME CLOCKS, SETS SOME TIMERS ETC.)
- AFTER A DELAY DEFINED BY A PASSIVE RC NETWORK, THE VDD REG IS ENABLED
Note 04
HIGH
- LP_STOP MODE IS REQUESTED
PWR_LP
CORE SUPPLY Enable Output
OFF
- WHEN PWRLP_TEMPO ELAPSES, THE APPLICATION ENTER RUN MODE
OUTPUT
PWR_ONRST
PDR_ON
VTT POWER PLANE RULES [AN5122] [P.27]
- THE MPU ENTERS RUN MODE
- THE MPU IS KEPT IN INTERNAL RESET AS LONG AS THE TIMER IS ACTIVE
- ONCE VDD IS STABLE AND ABOVE THE THRESHOLD LEVEL, A TIMER [tRSTTEMPO] IS STARTED
- DEPENDING ON THE USB ACTIVITY, THE SOFTWARE MAY TURN VDDA1V8_REG ON OR OFF
Q1 MOSFET SELECTION - KEY PARAMETERS
STABLE
- VDD_DDR, VREF_DDR, VTT AND VDD_PERIPH ARE POWERED OFF BY THE PWR_ONRST SIGNAL
< 20 pF
- THE VDD_1V8REG INTERNAL REGULATOR IS ENABLED AND ITS VOLTAGE STARTS RISING
- PWR_ON AND PWR_LP ARE DRIVEN HIGH
- THE SOFTWARE MAY SWITCH OFF THE USB POWER BT TURNING OFF VDDA1V8REG
THE "AND GATE" IS USED TO SHARPEN THE EDGE OF THE USB_REG_EN SIGNAL. IT COULD BE REMOVED AND BRIDGED BY INSTALLING A 0402 0 OHM RESISTOR ON THE PADS BELOW IT.
PD / PU
POWER-UP SEQUENCE MANAGEMENT
BOOT CAP - DIODE [DS6206A-03] [P.13]
MECHANICAL / FIDUCIALS
- ONCE TIMER [tRSTTEMPO] ELAPSES, [PWR_ON] and [PWR_LP] ARE SET HIGH BY THE MPU
- VDD VOLTAEG STARTS RISING
VTT
NRST
N-CHANNEL MOSFET
PLACE NEAR IC
- [PWR_ON] [PWR_LP] [NRST] - SET LOW BY THE MPU, FORCING [PWR_ONRST] LOW
1. ONE HF CAPACITOR MUST BE RESERVED FOR TWO RTT TERMINATION RESISTORS AND MUST BE PLACED AS CLOSE AS POSSIBLE TO THEM. 2. BULK CAPACITORS CAN BE PLACED ANYWHERE BETWEEN THE VTT REGULATOR AND TERMINATIONS. 3. LEAVE SUFFICIENT SPACING AROUND VTT ISLAND TO REDUCE CROSSTALK
Note 02
PWR_ON
Note 01
No Internal Pullups
PDR_ON_CORE
INPUT
*USED AS VDD_USB REGULATOR ENABLE
TRM P.123
- TIMER ELAPSES
POWER CONTROL & RESET PINS OVERVIEW
2. IDSS:
- VIN STARTS RISING
- ONCE THE HSI CLOCK IS STABLE [5uS], PWRLP_TEMPO [TIMER][MIN-100uS] IS STARTED
VIN STATUS
PLACE NEAR ICs
- A CLOCK RESTORE PROCESS IS PERFORMED
- RELEASING [NRST] MAKES [PWR_ONRST] TRANSITION TO A HIGH LEVEL
JTAG Reset
CORE SUPPLY LP Stop Mode Selection Output
- EADLY [TIMER] IS STARTED
VDD POR Enable
- PWR_ON AND PWR_LP ARE DRIVEN LOW
PLACE CLOSE TO DDR3L ICS
- THE VOLTAGE REGULATORS ARE ENABLED AND THEIR VOLTAGES START TO RISE
> 2 uA
< 2uA [CONDITIONS: VDS = 0.8V VGS = 0V]
- A VALID POWER SOURCE IS CONNECTED
- THE PWR_LP SIGNAL IS ASSERTED (LOW)
STANDBY MODE
NJTRST
- VTT ENTERS LOW POWER MODE (HIGH-IMPEDANCE)
LOW
12C PULLUPS
VDDPERIPH
1. C101 - THIS CAPACITOR PROVIDES THE GATE DRIVER VOLTAGE FOR THE HIGH SIDE MOSFET. 2. D101 - IT IS RECOMMENDED TO ADD THIS DIODE FOR EFFICIENCY IMPROVEMENT IF THE BOARD VIN = 5V OR DUTY RATIO IS HIGHER THAN 65%
- IT THEN SETS THE [LPDS REGISTER] TO ENTER LP-STOP MODE
- AFTER TIMER [tRSTTEMPO] ELAPSES, THE MPU WAITS FOR 20 uS BEFORE RELASING [NRST]
- THE MPU IS KEPT IN INTERNAL RESET UNTIL THE TIMER ELAPSES
- WHEN ITS VOLTAGE REACHES THE VDDUSB REG EN THRESHOLD, VDDUSB REG IS ENABLED
- THE VDDCORE REGULATOR IS ENABLED BY THE [PWR_ON] SIGNAL AND VDDCORE STARTS RISING
- WHEN EADLY [TIMER] IT ELAPSES, THE BOOT ROM STARTS ACCESSING THE EXT. MEMORY
LAYER CHANGE CAPACITORS [AN5122] [P.19-20]
JTAG CONNECTOR
- AFTER IT ELAPSES, THE BOOT ROM STARTS ACCESSING THE EXTERNAL PERIPHERALS
REFER TO THE "L&C&R VALUES" SPREADSHEET IN THE PROJECT FOLDER FOR INFORMATION ON HOW THE INDUCTOR, CAPACITOR AND RESISTOR VALUES ARE CALCULATED FOR EACH IC.
APP Pad Reset INPUT / OUTPUT
DESCRIPTION
- VTT REG EXITS LOW POWER MODE
1. TYPE:
I/O
6. CRSS:
- THE SOFTWARE PREPARES AN LP_STOP ENTRY (STOPS SOME CLOCKS, DDR SELF-REFRESH ETC.)
3. VGS(TH):
WAKEUP
22R
< 1.8V [SHOULD BE BELOW VDD_CPU V]
NRST_CORE - TO BE USED WHEN "VDD_CORE POR" IS DISABLED
- ONCE THE TIMER ELAPSES, THE MPU IS TAKEN OUT OF INTERNAL RESET
LP-STOP MODE
VDD_DDR
- ONCE VDDCORE IS STABLE AND ABOVE THE THRESHOLD LEVEL, A TIMER IS STARTED
- ONCE VDDCORE VOLTAGE IS ABOVE THE THRESHOLD, tVDDCORETEMPO [TIMER] IS STARTED
VREF_DDR
- THE VTT VOLTAGE SHOULD BE STABLE BEFORE THE TIMER ELAPSES
PIN NAME
VDD_PERIPH
- PWR_ONRST ALSO RISES, AS BOTH PWR_ON AND NRST ARE HIGH
ACTIVE
- WHEN THE SOFTWARE IS READY, IT ENTERS STANDBY MODE AND THE POPL[TIMER] STARTS
VDDUSB
4. ID MIN:
- STANDBY MODE IS REQUESTED
VDD_CORE
WHEN A SENSITIVE SIGNAL SWITCHES REFERENCE PLANES, A 100nF CAPACITOR MUST BE PLACED AS CLOSE AS POSSIBLE TO THE SIGNAL VIA, IN ORDER TO PROVIDE A HF RETURN CURRENT REFERENCE PATH TO THE SIGNAL. THE CAPACITOR CAN BE PLACED ON EITHER THE TOP OR BOTTOM LAYER OF THE PCB.
1. C581 - THIS CAPACITOR PROVIDES THE GATE DRIVER VOLTAGE FOR THE HIGH SIDE MOSFET. 2. D530 - IT IS RECOMMENDED TO ADD THIS DIODE FOR EFFICIENCY IMPROVEMENT IF THE BOARD VIN = 5V OR DUTY RATIO IS HIGHER THAN 65%
RF MATCHING NETWORK
- [PWR_ONRST] ENABLES THE VDDPERIPH, VDDDDR, VTT AND THEIR VOLTAGES START RISING
- THE VDDCORE REGULATOR IS POWERED OFF BY THE PWR_ON SIGNAL
APPLICATION NOT POWERED OR IN VBAT MODE
R10K
1. THE VBAT PIN CAN BE CONNECTED TO AN EXTERNAL BATTERY [1.2V < VBAT < 3.6V] 2. IF NO EXTERNAL BATTERY IS USED, IT IS MANDATORY TO CONNECT THIS PIN TO VDD_CPU. 3. DECOUPLE WITH 100nF CAPACITOR IF A BATTERY IS USED [NO DECOUPLING CAP REQUIRED] IF CONNECTED TO VDD_CPU OR A SUPERCAPACITOR].
- THE [EADLY][10uS] DELAY TIMER IS STARTED
VDDCORE POR Enable
VDD
VBAT [DS12504] [P.28] [3.8.1]
VDDA1V8_REG
- THE MPU PERFORMS AN INTERNAL HARDWARE INITIALISATION
- ON A WAKEUP EVENT, THE MPU LEAVES STANDBY MODE
THE APPLICATION IS POWERED AND RUNNING
- MPU LEAVES LP_STOP MODE AND DE ASSERTS PWR_LP
> 0.8V
- THE MPU IS TAKEN OUT OF INTERNAL RESET AND PERFORMS INTERNAL HW INITIALISATION
- AFTER THE HARDWARE INITIALISATION IS COMPLETE, THE MPU ENTER "RUN MODE"
